ramithuh/Pulse-Sensor/IMG_2769.PNG

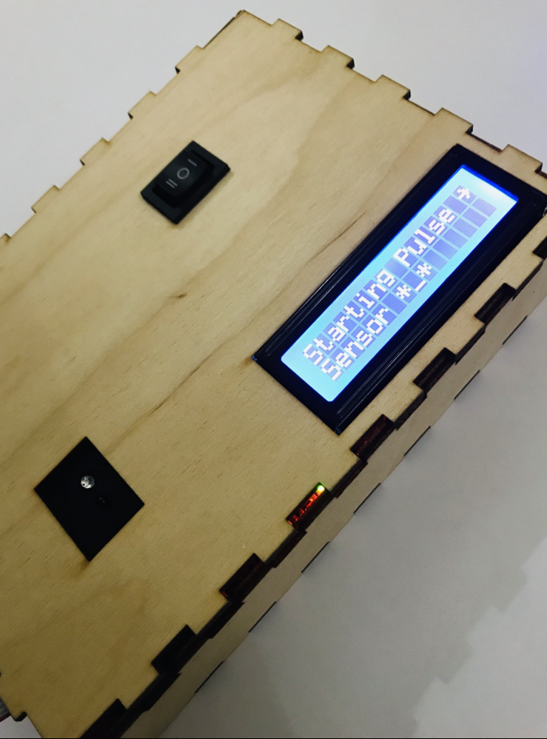
IMG_2769.PNG
