ramithuh/Pulse-Sensor/IMG_2770.jpg

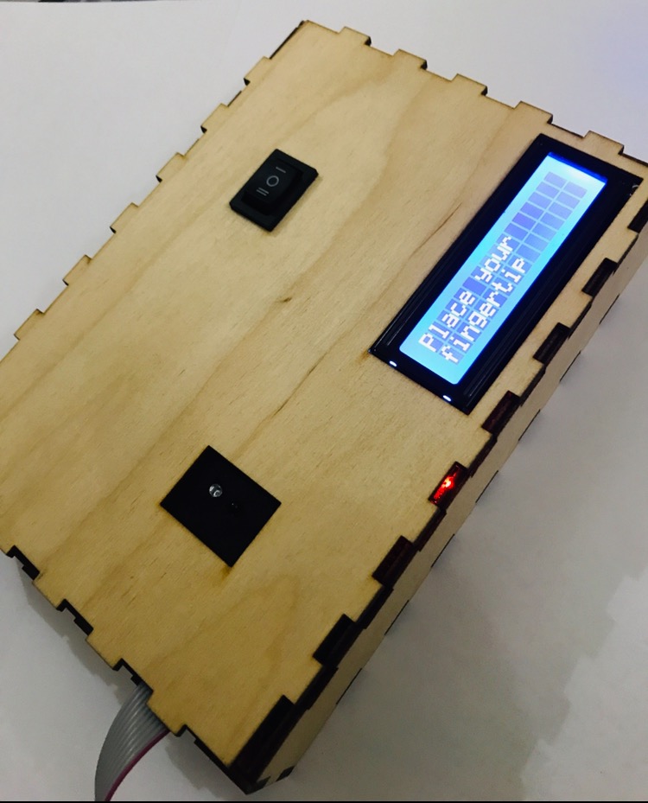
IMG_2770.jpg
