ramithuh/Pulse-Sensor/latex_project_report/images/0-8.jpg

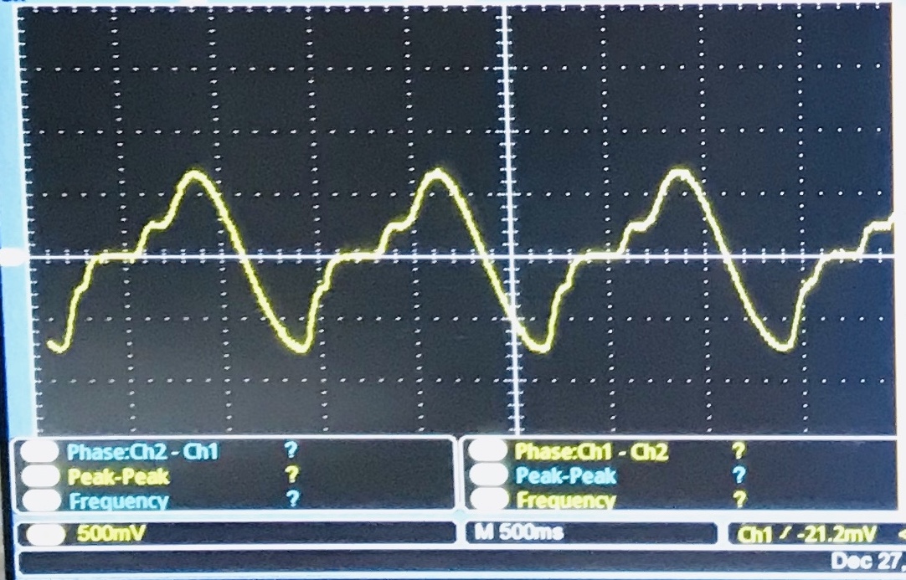
latex_project_report/images/0-8.jpg
